TinyCircuits/TinyCircuits-TinyScreenPlus-ASM2022/cad/TinyScreenPlus_ASM2022_REV4-DETAILED_DRAWING-PNG.png

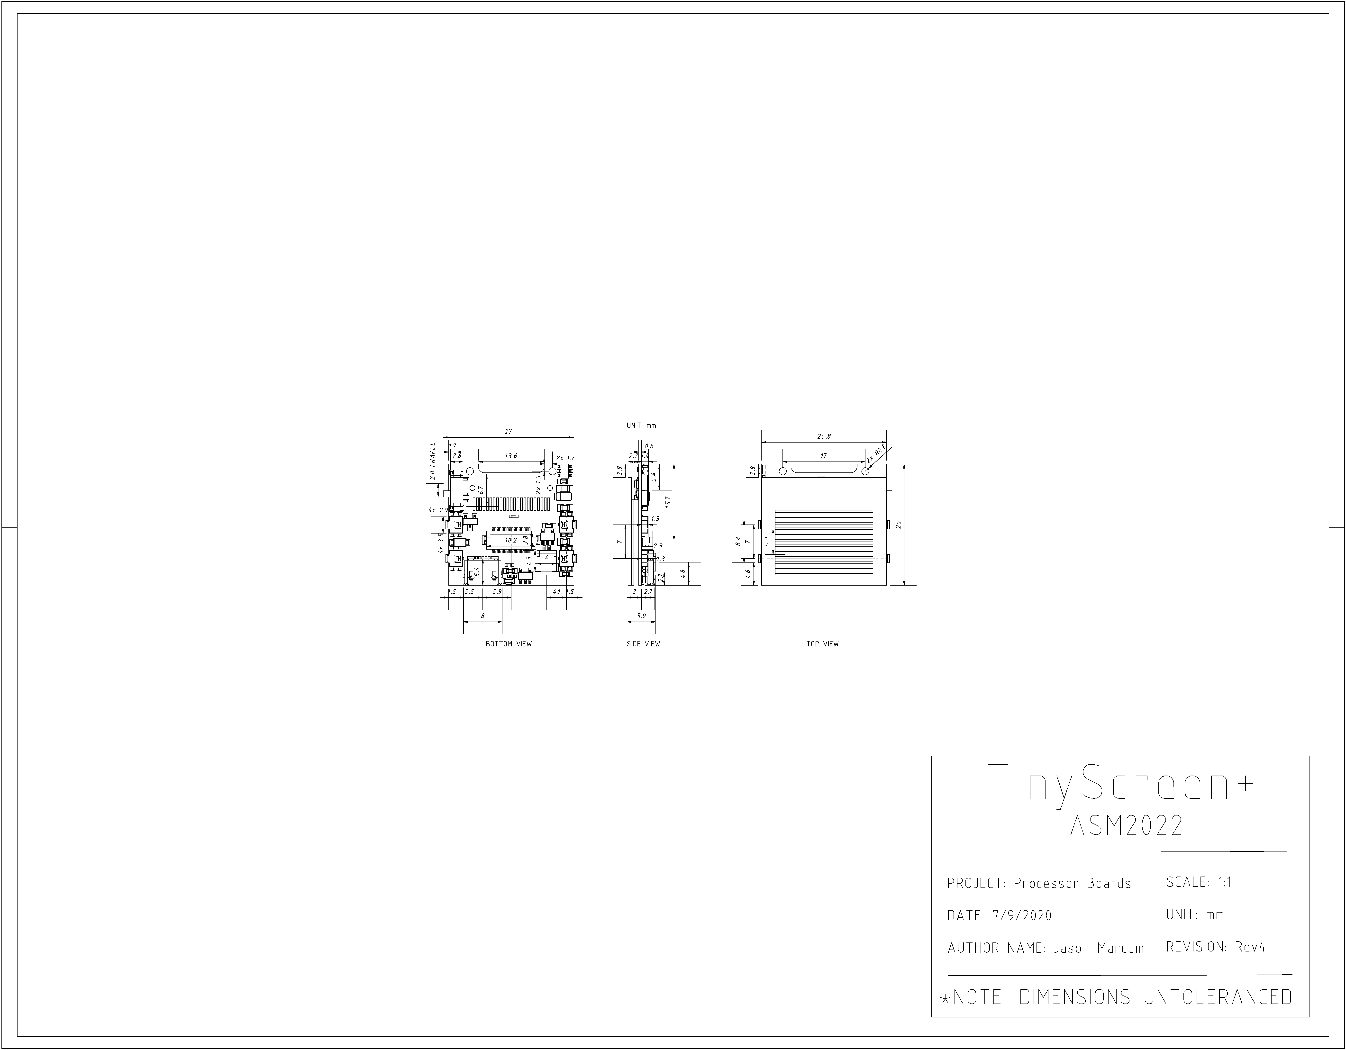
cad/TinyScreenPlus_ASM2022_REV4-DETAILED_DRAWING-PNG.png
