TinyCircuits/TinyCircuits-TinyScreenPlus-ASM2022/images/ASD2431-R-Tutorial-Animation-01.gif

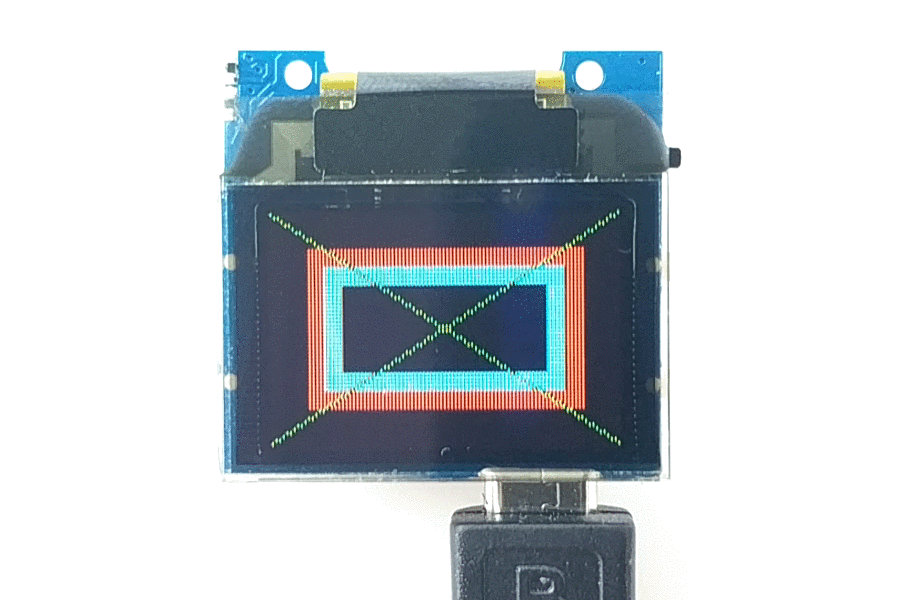
images/ASD2431-R-Tutorial-Animation-01.gif
