TinyCircuits/TinyCircuits-TinyScreenPlus-ASM2022/images/ASM2022-Tutorial-Image-01.png

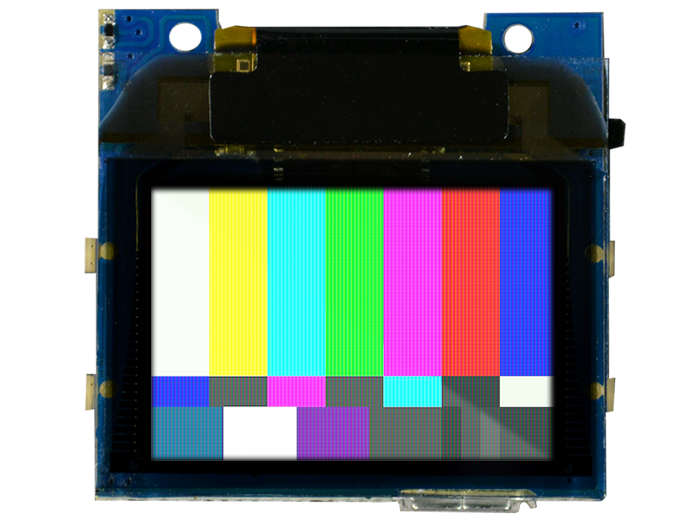
images/ASM2022-Tutorial-Image-01.png
