TinyCircuits/TinyCircuits-TinyScreenPlus-ASM2022/images/ASM2022-Tutorial-Image-02.jpg

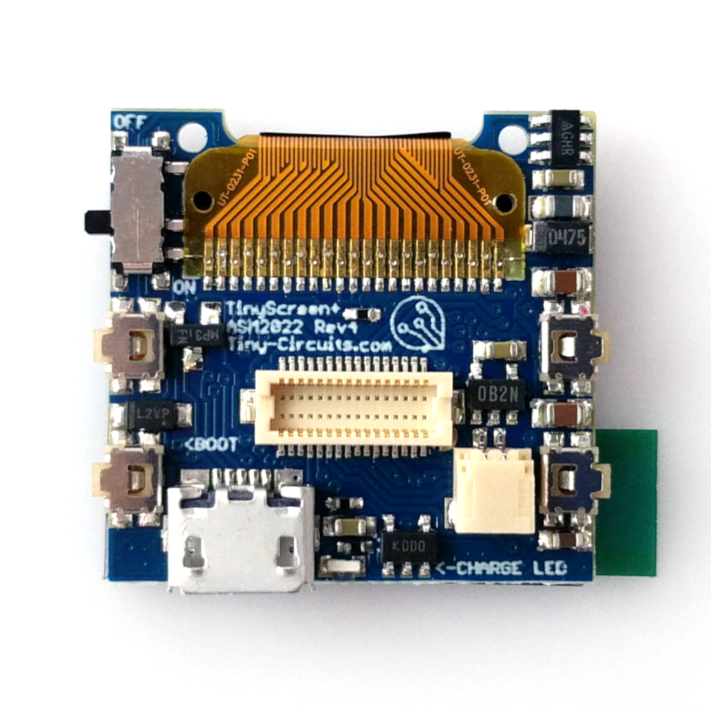
images/ASM2022-Tutorial-Image-02.jpg
