TinyCircuits/TinyCircuits-TinyScreenPlus-ASM2022/images/tutorial_images/ASM2022-Tutorial-Image-02.jpg

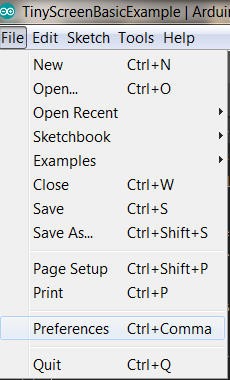
images/tutorial_images/ASM2022-Tutorial-Image-02.jpg
