TinyCircuits/TinyCircuits-TinyScreenPlus-ASM2022/images/tutorial_images/ASM2022-Tutorial-Image-10.png

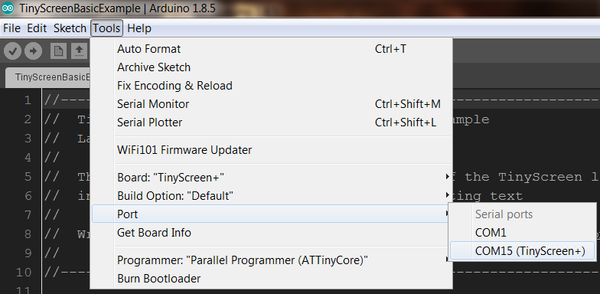
images/tutorial_images/ASM2022-Tutorial-Image-10.png
